oinetsrv/40-PROJETO-TACOMETRO-V-1-2/DIAGRAMAS E IMAGENS/DIAGRAMA-PCB-I-O-P1.jpg

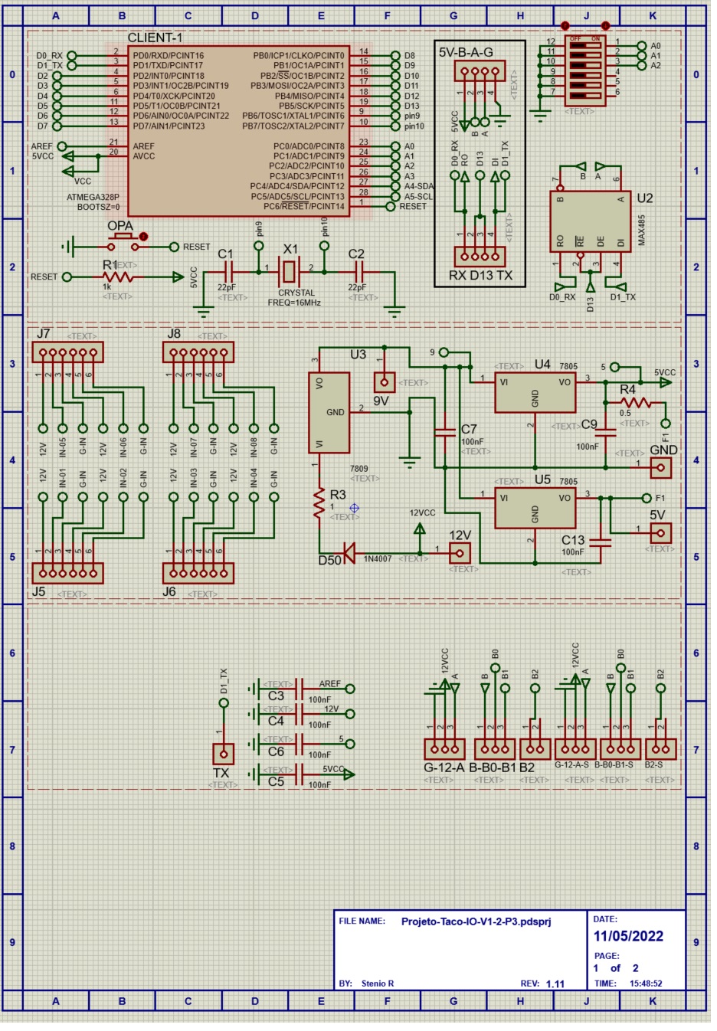
DIAGRAMAS E IMAGENS/DIAGRAMA-PCB-I-O-P1.jpg
