oinetsrv/40-PROJETO-TACOMETRO-V-1-2/MODELAGEM 3D/versoes anteriores/PCB-REDE-V1_4 3D FUROS.STL

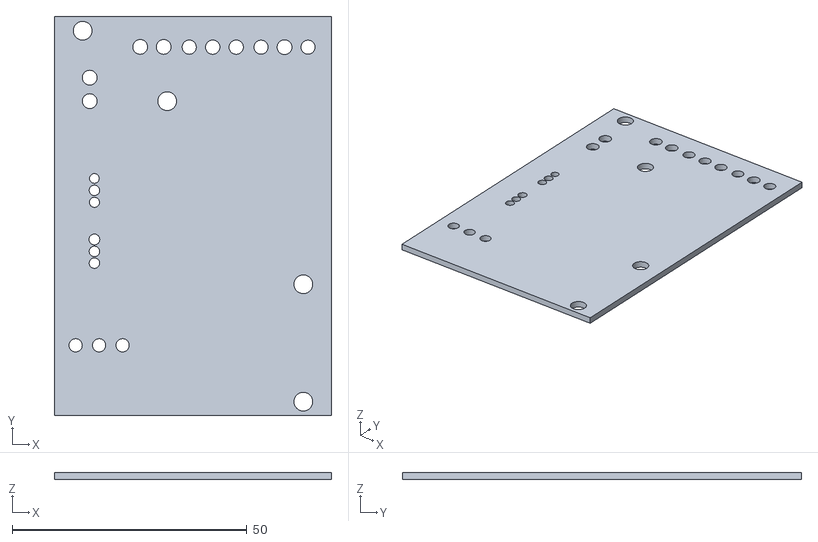
[picture p23: CAD file, 2022-08-12]
MODELAGEM 3D/versoes anteriores/PCB-REDE-V1_4 3D FUROS.STL
59.0 x 85.0 x 1.58
