oinetsrv/40-PROJETO-TACOMETRO-V-1-2/MODELAGEM 3D/versoes anteriores/COLAR-P2-V2.SLDPRT

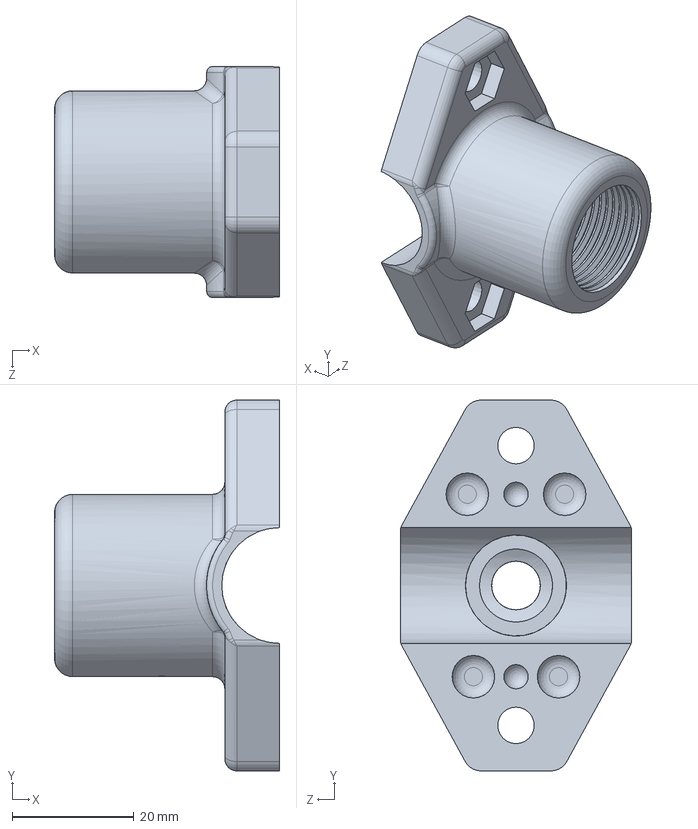
[picture p24: CAD file, 2022-06-17]
MODELAGEM 3D/versoes anteriores/COLAR-P2-V2.SLDPRT
37.0 x 61.0 x 38.0 mm
